philcrump/scot-resolver/firmware/config.h

#ifndef __CONFIG_H__
#define __CONFIG_H__

/*
extern uint8_t config_device_id[12];
extern char config_device_id_hexstr[25];

extern uint32_t config_can_address_prefix;
extern char config_can_address_prefix_hexstr[5];
*/

void config_init(void);

#endif /* __CONFIG_H__ */
